ioanaior/E-Book_ReaderTSC/Images/Screenshot 2025-04-06 160542.png

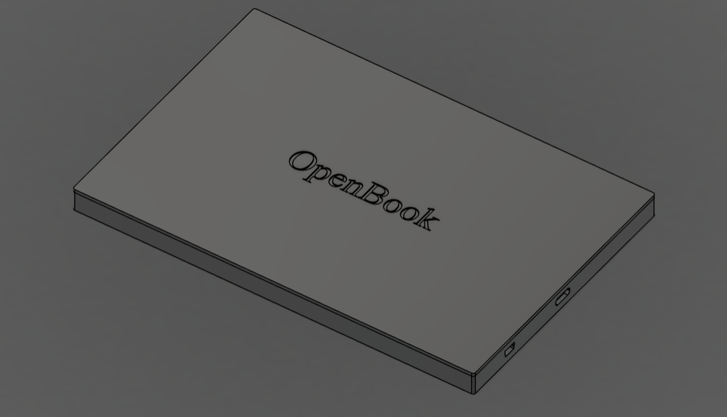
Images/Screenshot 2025-04-06 160542.png
