ioanaior/E-Book_ReaderTSC/Images/Screenshot 2025-04-06 160732.png

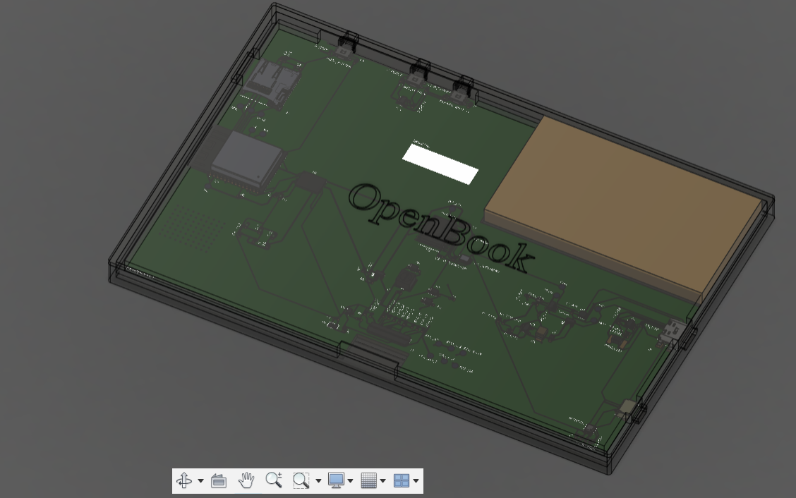
Images/Screenshot 2025-04-06 160732.png
