ioanaior/E-Book_ReaderTSC/Images/Screenshot 2025-04-06 160811.png

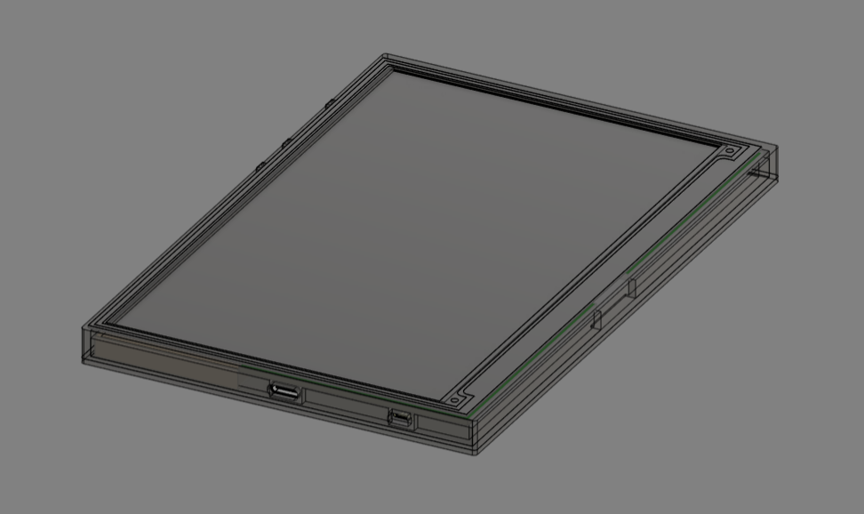
Images/Screenshot 2025-04-06 160811.png
